Ramon-Esteve/polyphonic-synth/docs/bringup_vco_v2/photos/IMG_1949.jpeg

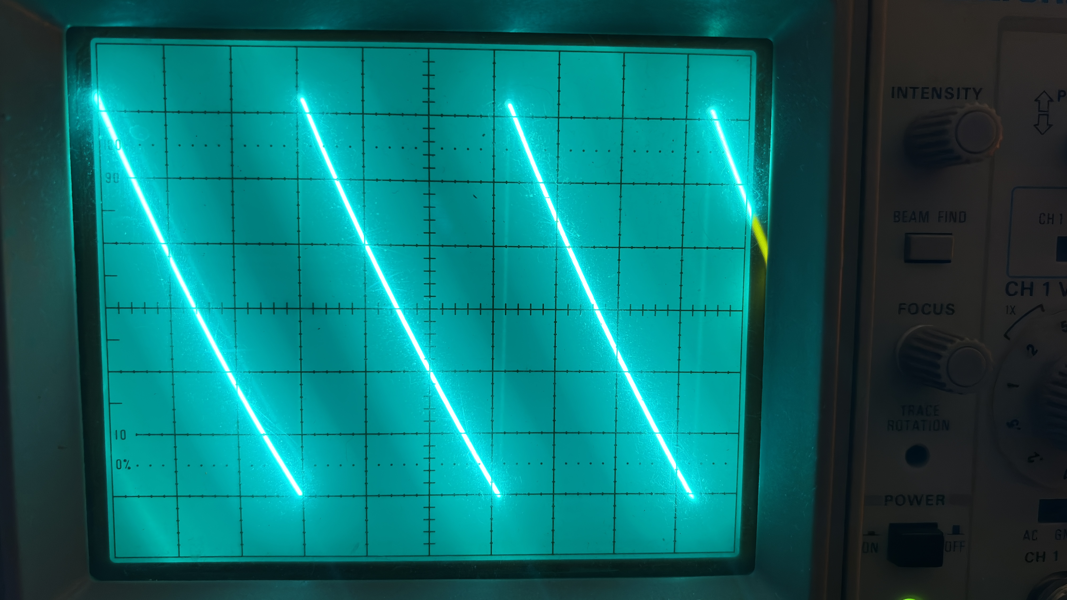
docs/bringup_vco_v2/photos/IMG_1949.jpeg
