Ramon-Esteve/polyphonic-synth/hardware/poly_synth_main/SYNTHH.kicad_sch

## KiCad design hardware/poly_synth_main/SYNTHH.kicad_sch (2026-06-09)

Schematic: SYNTHH.kicad_sch

Parts:
A1, A2: 10k; Potentiometer_Bourns_PTA6043_Single_Slide
ADJ_TUNE1, ADJ_TUNE2, ADJ_TUNE3: 1k; Potentiometer_Bourns_3266W_Vertical
AUDIO_OUT(3.5mm)1: AudioJack2_Ground_Switch; Jack_3.5mm_Cliff_FCR1281_Horizontal
C1, C10, C15: 2.2nF; C_Rect_L13.0mm_W4.0mm_P10.00mm_FKS3_FKP3_MKS4
C2, C11, C16: 1uF; C_Rect_L7.2mm_W5.0mm_P5.00mm
C3, C4, C5, C8, C9, C12, C13, C14, C17, C18, C19, C20, C21, C28, C29, C31, C32, C35, C36, C37, C38, C39, C40, C41, C42, C43, C44: 0.1uF; C_Disc_D5.1mm_W3.2mm_P5.00mm
C6, C7: 47uF; C_Radial_D5.0mm_H11.0mm_P2.00mm
C22, C30, C45: 1uF
C23, C24, C25, C26, C27: 1nF
C33: 0.33uF
C34: 0.1uF
COARSE1, COARSE2, COARSE3: 100k; Potentiometer_Omeg_PC16BU_Vertical
CUTOFF1: 100k; Potentiometer_Omeg_PC16BU_Vertical
CV_IN5: AudioJack2_Ground_Switch; Jack_3.5mm_Cliff_FCR1281_Horizontal
D1, D4, D5, D6, D7, D8, D9, D10, D11, D12, D13, D14, D15, D16: 1N4148; D_DO-35_SOD27_P7.62mm_Horizontal
D2, D3, D18, D19, D20: SB140; D_DO-41_SOD81_P10.16mm_Horizontal
D17, D21: 10k; Potentiometer_Bourns_PTA6043_Single_Slide
FINE1, FINE2, FINE3: 100k; Potentiometer_Omeg_PC16BU_Vertical
FM_IN3: AudioJack2_Ground_Switch; Jack_3.5mm_Cliff_FCR1281_Horizontal
FM_LVL3: 1M; Potentiometer_Omeg_PC16BU_Vertical
J1: DC_IN; TerminalBlock_RND_205-00288_1x03_P5.08mm_Horizontal
J2: USB_B
J3: AUDIO_OUT(6.35mm)
OFFSET1: 100k; Potentiometer_Omeg_PC16BU_Vertical
PWM1, PWM2, PWM3: 100k; Potentiometer_Omeg_PC16BU_Vertical
PWM_CV_LVL1, PWM_CV_LVL2, PWM_CV_LVL3: 250k; Potentiometer_Omeg_PC16BU_Vertical
PWM_IN1, PWM_IN2, PWM_IN3: AudioJack2_Ground_Switch; Jack_3.5mm_Cliff_FCR1281_Horizontal
Q1, Q4, Q6, Q7, Q8: BC548; TO-92_Inline
Q2, Q3, Q5: BC558; TO-92_Inline
Q-Point(Forward_Bias)1: 100k
R1, R5, R27, R31, R47, R51: 1M; R_Axial_DIN0207_L6.3mm_D2.5mm_P10.16mm_Horizontal
R2, R30, R50: 1k5; R_Axial_DIN0207_L6.3mm_D2.5mm_P10.16mm_Horizontal
R3, R22, R29, R32, R52, R62, R70, R71, R72, R74, R75, R76, R87, R89, R94, R96, R99, R100, R101, R103, R104, R105, R106, R107, R108, R110, R111, R112, R117, R118, R125, R126, R127, R128, R129, R132, R133, R134, R136, R137: 100k
R4, R6, R8, R9, R10, R12, R14, R19, R23, R25, R26, R28, R33, R34, R38, R39, R43, R45, R46, R48, R49, R53, R54, R58, R59: 100k; R_Axial_DIN0207_L6.3mm_D2.5mm_P10.16mm_Horizontal
R7, R24, R44: 33k; R_Axial_DIN0207_L6.3mm_D2.5mm_P10.16mm_Horizontal
R11, R37, R57: 47k; R_Axial_DIN0207_L6.3mm_D2.5mm_P10.16mm_Horizontal
R13, R16, R41, R63, R64, R65, R66, R67, R68, R69, R114, R138: 10k
R15, R17, R35, R40, R55, R60: 68k; R_Axial_DIN0207_L6.3mm_D2.5mm_P10.16mm_Horizontal
R18, R36, R56: 14k; R_Axial_DIN0207_L6.3mm_D2.5mm_P10.16mm_Horizontal
R20, R21: 10; R_Axial_DIN0207_L6.3mm_D2.5mm_P10.16mm_Horizontal
R42, R135: 10k; Potentiometer_Bourns_PTA6043_Single_Slide
R61, R78, R79, R81, R82, R83, R84, R85, R93: 33k
R73, R86: 27k
R77, R80: 2k
R88: 14k
R90, R91: 68k
R92, R95, R97, R130, R131: 1k
R98, R102, R109, R113, R123: 150k
R115, R116: 20k_Matched
R119, R120: 10k_MATCHED
R121, R122: 100k_MATCHED
R124: 100
RESO1: 100k; Potentiometer_Omeg_PC16BU_Vertical
RV1: 20k
R_pull_UP_SCL1: 4.7k
R_pull_UP_SDA1: 4.7k
S1, S2: 10k; Potentiometer_Bourns_PTA6043_Single_Slide
SOFTCLIP1: 100k; Potentiometer_Omeg_PC16BU_Vertical
SW1, SW3, SW5: SAW; Nidec_Copal_CAS-120A
SW2, SW4, SW6: PULSE; Nidec_Copal_CAS-120A
SW7: SUB; Nidec_Copal_CAS-120A
TH2, TH3, TH4, TH5, TH6, TH7, TH9, TH10, TH11, TH12: 10k; R_Axial_DIN0204_L3.6mm_D1.6mm_P5.08mm_Horizontal
U1: 40106; DIP-14_W7.62mm_Socket
U2, U4, U6: TL074; DIP-14_W7.62mm_Socket
U3, U5, U7, U8, U11, U13, U14, U15, U17: TL074
U9: NUCLEO-F446RE; MODULE_NUCLEO-F446RE; PARTREV 13
U10: L7805
U12: MCP4728; MSOP-10_3x3mm_P0.5mm
U16: ER_OLEDM0.91_1x-I2C
VCO1, VCO2, VCO3, VCO5, VCO6: 100k; Potentiometer_Omeg_PC16BU_Vertical
reso_intensity1: 50k; Potentiometer_Omeg_PC16BU_Vertical

Connections:
32DAC1 PA4: U9.CN7_32 (PA4), U13.2 (-)
+3.3V: A1.1, A2.1, D17.1, D18.2 (A), D19.2 (A), D20.2 (A), D21.1, R42.1, R135.1, R137.1, R_pull_UP_SCL1.1, R_pull_UP_SDA1.1, S1.1, S2.1, U9.CN7_16 (CN7_+3V3), U12.1 (VDD), U16.2 (VCC)
+12V: C3.1, C5.1, C6.1, C8.1, C12.1, C13.1, C18.1, C20.1, C28.1, C31.1, C33.2, C35.1, C37.1, C39.1, C41.1, C44.1, CUTOFF1.1, PWM1.1, PWM2.1, PWM3.1, Q-Point(Forward_Bias)1.1, R1.1, R9.2, R20.2, R23.2, R31.1, R43.2, R51.1, R115.1, R116.1, R128.1, U1.14 (VDD), U2.4 (V+), U3.4 (V+), U4.4 (V+), U5.4 (V+), U6.4 (V+), U7.4 (V+), U8.11 (V-), U10.1 (IN), U11.4 (V+), U13.4 (V+), U14.11 (V-), U15.4 (V+), U17.4 (V+)
-12V: C4.2, C7.2, C9.2, C14.2, C17.2, C19.2, C21.2, C29.2, C32.2, C36.2, C38.2, C40.2, C42.2, C43.2, CUTOFF1.3, PWM1.3, PWM2.3, PWM3.3, Q2.1 (C), Q3.1 (C), Q5.1 (C), Q-Point(Forward_Bias)1.3, R6.1, R7.1, R21.2, R24.1, R25.1, R44.1, R45.1, R87.1, U2.11 (V-), U3.11 (V-), U4.11 (V-), U5.11 (V-), U6.11 (V-), U7.11 (V-), U8.4 (V+), U11.11 (V-), U13.11 (V-), U14.4 (V+), U15.11 (V-), U17.11 (V-)
FEEDBACK: C23.1, C27.1, D15.2 (A), D16.1 (K), R96.1, U8.8
GND: A1.3, A2.3, ADJ_TUNE1.1, ADJ_TUNE1.2, ADJ_TUNE2.1, ADJ_TUNE2.2, ADJ_TUNE3.1, ADJ_TUNE3.2, AUDIO_OUT(3.5mm)1.G, AUDIO_OUT(3.5mm)1.S, C1.2, C3.2, C4.1, C5.2, C6.2, C7.1, C8.2, C9.1, C10.2, C12.2, C13.2, C14.1, C15.2, C17.1, C18.2, C19.1, C20.2, C21.1, C24.1, C25.1, C26.1, C28.2, C29.1, C31.2, C32.1, C33.1, C34.1, C35.2, C36.1, C37.2, C38.1, C39.2, C40.1, C41.2, C42.1, C43.1, C44.2, CV_IN5.G, CV_IN5.S, CV_IN5.T, D17.3, D21.3, FINE1.1, FINE2.1, FINE3.1, FM_IN3.G, FM_IN3.S, J1.2, J2.4 (GND), J2.SH (Shield), J3.S, OFFSET1.3, PWM_IN1.G, PWM_IN1.S, PWM_IN2.G, PWM_IN2.S, PWM_IN3.G, PWM_IN3.S, Q1.3 (E), Q4.3 (E), Q6.3 (E), R10.1, R11.1, R15.2, R18.1, R34.1, R36.1, R37.1, R40.2, R42.3, R54.1, R56.1, R57.1, R60.2, R73.1, R77.1, R84.2, R86.2, R94.2, R97.2, R117.2, R121.2, R124.2, R135.3, R136.1, RESO1.3, RV1.1, RV1.2, S1.3, S2.3, U1.7 (VSS), U1.9, U1.11, U1.13, U3.12 (+), U5.12 (+), U7.3 (+), U7.10 (+), U8.3 (+), U9.CN7_8 (CN7_GND), U9.CN7_19 (CN7_GND), U9.CN7_20 (CN7_GND), U9.CN7_22 (CN7_GND), U10.2 (GND), U12.4 (~LDAC), U12.10 (VSS), U14.3 (+), U14.5 (+), U15.3 (+), U16.1 (GND), U17.2 (-), U17.6 (-), U17.9 (-), U17.12 (+), VCO1.3, VCO2.3, VCO3.3, VCO5.3, VCO6.1, VCO6.3
MIXER: R3.1, R22.2, R29.2, R32.2, U3.13 (-)
unnamed: A1.2, U9.CN7_38 (PC0/PB8)
unnamed: A2.2, U9.CN7_28 (PA0)
unnamed: ADJ_TUNE1.3, R2.2
unnamed: ADJ_TUNE2.3, R30.2
unnamed: ADJ_TUNE3.3, R50.2
unnamed: AUDIO_OUT(3.5mm)1.T, R130.2
unnamed: C1.1, D1.1 (K), Q1.1 (C), U1.1, U2.3 (+)
unnamed: C2.1, U2.1, U2.2 (-)
unnamed: C2.2, R10.2, U2.5 (+), U2.10 (+)
unnamed: C10.1, D6.1 (K), Q4.1 (C), U1.3, U4.3 (+)
unnamed: C11.1, U4.1, U4.2 (-)
unnamed: C11.2, R34.2, U4.5 (+), U4.10 (+)
unnamed: C15.1, D8.1 (K), Q6.1 (C), U1.5, U6.3 (+)
unnamed: C16.1, U6.1, U6.2 (-)
unnamed: C16.2, R54.2, U6.5 (+), U6.10 (+)
unnamed: C22.1, U5.6 (-), U5.7
unnamed: C22.2, R76.1
unnamed: C23.2, D7.1 (K), D9.2 (A)
unnamed: C24.2, D9.1 (K), D10.2 (A)
unnamed: C25.2, D10.1 (K), D11.2 (A), U7.12 (+)
unnamed: C26.2, D11.1 (K), D12.2 (A)
unnamed: C27.2, D12.1 (K), D13.2 (A)
unnamed: C30.1, R93.2, U8.1
unnamed: C30.2, R94.1, U8.5 (+)
unnamed: C34.2, U9.CN7_6 (E5V), U10.3 (OUT)
unnamed: C45.1, R130.1, U15.8, U15.9 (-)
unnamed: C45.2, R62.1
unnamed: COARSE1.1, R9.1
unnamed: COARSE1.2, R8.1
unnamed: COARSE1.3, R7.2
unnamed: COARSE2.1, R23.1
unnamed: COARSE2.2, R26.1
unnamed: COARSE2.3, R24.2
unnamed: COARSE3.1, R43.1
unnamed: COARSE3.2, R46.1
unnamed: COARSE3.3, R44.2
unnamed: CUTOFF1.2, R89.1
unnamed: D1.2 (A), U1.2
unnamed: D2.1 (K), R20.1
unnamed: D3.2 (A), R21.1
unnamed: D4.1 (K), D5.2 (A), RV1.3
unnamed: D4.2 (A), D5.1 (K), R71.2, U5.3 (+)
unnamed: D6.2 (A), U1.4
unnamed: D7.2 (A), R79.2, R80.2
unnamed: D8.2 (A), U1.6
unnamed: D13.1 (K), R82.2, U7.7
unnamed: D14.1 (K), R81.1, R85.1, R86.1, R87.2
unnamed: D14.2 (A), R88.2, U7.8
unnamed: D15.1 (K), D16.2 (A), R96.2, U8.9 (-), reso_intensity1.3
unnamed: D17.2, U9.CN7_36 (PC1/PB9)
unnamed: D18.1 (K), R13.2, U9.CN10_4 (PC6)
unnamed: D19.1 (K), R16.2, U9.CN10_19 (PC7)
unnamed: D20.1 (K), R41.2, U9.CN10_2 (PC8)
unnamed: D21.2, U9.CN7_30 (PA1)
unnamed: FINE1.2, R5.1
unnamed: FINE1.3, R6.2
unnamed: FINE2.2, R27.1
unnamed: FINE2.3, R25.2
unnamed: FINE3.2, R47.1
unnamed: FINE3.3, R45.2
unnamed: FM_IN3.T, R49.1
unnamed: FM_LVL3.1, TH12.1
unnamed: FM_LVL3.2, FM_LVL3.3, Q5.2 (B), R50.1, TH9.1, TH10.1, TH11.1
unnamed: J2.2 (D-), U9.CN10_14 (PA11)
unnamed: J2.3 (D+), U9.CN10_12 (PA12)
unnamed: J3.T, R131.2
unnamed: OFFSET1.1, R128.2
unnamed: OFFSET1.2, R127.1
unnamed: PWM1.2, R19.1
unnamed: PWM2.2, R33.1
unnamed: PWM3.2, R53.1
unnamed: PWM_CV_LVL1.1, PWM_IN1.T
unnamed: PWM_CV_LVL1.2, PWM_CV_LVL1.3, R17.1
unnamed: PWM_CV_LVL2.1, PWM_IN2.T
unnamed: PWM_CV_LVL2.2, PWM_CV_LVL2.3, R35.1
unnamed: PWM_CV_LVL3.1, PWM_IN3.T
unnamed: PWM_CV_LVL3.2, PWM_CV_LVL3.3, R55.1
unnamed: Q1.2 (B), Q2.3 (E), R1.2
unnamed: Q2.2 (B), R2.1, TH2.1, TH3.1, TH4.1
unnamed: Q3.2 (B), R30.1, TH5.1, TH6.1, TH7.1
unnamed: Q3.3 (E), Q4.2 (B), R31.2
unnamed: Q5.3 (E), Q6.2 (B), R51.2
unnamed: Q7.1 (C), R115.2, R119.1
unnamed: Q7.2 (B), R117.1, R118.2
unnamed: Q7.3 (E), Q8.3 (E), R114.1
unnamed: Q8.1 (C), R116.2, R120.1
unnamed: Q8.2 (B), R124.1, R125.1
unnamed: Q-Point(Forward_Bias)1.2, R125.2
unnamed: R3.2, R52.1, U3.14
unnamed: R4.2, TH2.2
unnamed: R5.2, TH3.2
unnamed: R8.2, TH4.2
unnamed: R11.2, R12.2, U2.6 (-)
unnamed: R12.1, R64.1, U2.7
unnamed: R13.1, U17.1
unnamed: R14.1, R15.1, U2.12 (+)
unnamed: R14.2, U2.8
unnamed: R16.1, U17.7
unnamed: R17.2, R18.2, R19.2, U2.9 (-)
unnamed: R22.1, VCO1.2
unnamed: R26.2, TH5.2
unnamed: R27.2, TH6.2
unnamed: R28.2, TH7.2
unnamed: R29.1, VCO2.2
unnamed: R32.1, VCO3.2
unnamed: R33.2, R35.2, R36.2, U4.9 (-)
unnamed: R37.2, R38.2, U4.6 (-)
unnamed: R38.1, R65.1, U4.7
unnamed: R39.1, R40.1, U4.12 (+)
unnamed: R39.2, U4.8
unnamed: R41.1, U17.8
unnamed: R42.2, U9.CN7_34 (PB0)
unnamed: R46.2, TH9.2
unnamed: R47.2, TH10.2
unnamed: R48.2, TH11.2
unnamed: R49.2, TH12.2
unnamed: R52.2, R70.1, U5.13 (-)
unnamed: R53.2, R55.2, R56.2, U6.9 (-)
unnamed: R57.2, R58.2, U6.6 (-)
unnamed: R58.1, R67.1, U6.7
unnamed: R59.1, R60.1, U6.12 (+)
unnamed: R59.2, U6.8
unnamed: R61.1, R62.2, U15.13 (-)
unnamed: R63.1, SW2.1 (C)
unnamed: R64.2, SW1.1 (C)
unnamed: R65.2, SW3.1 (C)
unnamed: R66.1, SW4.1 (C)
unnamed: R67.2, SW5.1 (C)
unnamed: R68.1, SW6.1 (C)
unnamed: R69.2, SW7.1 (C)
unnamed: R70.2, R71.1, R75.1, U5.14
unnamed: R72.1, R73.2, U5.2 (-)
unnamed: R72.2, R74.1, U5.1
unnamed: R74.2, SOFTCLIP1.3
unnamed: R75.2, SOFTCLIP1.1
unnamed: R76.2, R77.2, U5.10 (+)
unnamed: R78.1, R83.1, U5.8, U5.9 (-)
unnamed: R78.2, R79.1, R81.2, U7.2 (-)
unnamed: R80.1, U7.1
unnamed: R82.1, R83.2, U7.6 (-)
unnamed: R84.1, R85.2, U7.5 (+)
unnamed: R88.1, R89.2, R90.2, R91.2, U7.9 (-)
unnamed: R90.1, VCO5.2
unnamed: R91.1, VCO6.2
unnamed: R92.1, RESO1.1, U7.13 (-), U7.14
unnamed: R92.2, R93.1, U8.2 (-)
unnamed: R95.1, U8.6 (-), U8.7
unnamed: R97.1, reso_intensity1.1, reso_intensity1.2
unnamed: R98.1, R99.2, U11.1
unnamed: R98.2, U11.3 (+)
unnamed: R99.1, U11.6 (-)
unnamed: R100.1, R101.2, U11.7
unnamed: R100.2, U11.5 (+)
unnamed: R102.1, R103.2, U11.8
unnamed: R102.2, U11.10 (+)
unnamed: R103.1, U11.13 (-)
unnamed: R104.1, R105.2, U11.14
unnamed: R104.2, U11.12 (+)
unnamed: R106.2, R107.1, U13.14
unnamed: R107.2, U13.12 (+)
unnamed: R108.1, U13.13 (-)
unnamed: R108.2, R109.1, U13.8
unnamed: R109.2, U13.10 (+)
unnamed: R110.2, R111.1, U14.14
unnamed: R111.2, U14.12 (+)
unnamed: R112.1, U14.13 (-)
unnamed: R112.2, R113.1, U14.8
unnamed: R113.2, U14.10 (+)
unnamed: R114.2, R126.2, U15.1
unnamed: R119.2, R122.1, U8.13 (-)
unnamed: R120.2, R121.1, U8.12 (+)
unnamed: R122.2, U8.14, U15.5 (+), U15.10 (+)
unnamed: R123.1, R132.2, U13.1
unnamed: R123.2, U13.3 (+)
unnamed: R126.1, R127.2, R129.2, U15.2 (-)
unnamed: R131.1, U15.6 (-), U15.7
unnamed: R132.1, U13.6 (-)
unnamed: R133.1, R134.2, U13.7
unnamed: R133.2, U13.5 (+)
unnamed: R135.2, U9.CN7_37 (PC3)
unnamed: R136.2, R137.2, U15.12 (+)
unnamed: R61.2, R138.1, U15.14
unnamed: R138.2, U9.CN10_34 (PC4)
unnamed: RESO1.2, U8.10 (+)
unnamed: S1.2, U9.CN7_35 (PC2)
unnamed: S2.2, U9.CN10_37 (PA3)
unnamed: SOFTCLIP1.2, U5.5 (+)
unnamed: SW1.2 (B), SW2.2 (B), U3.3 (+)
unnamed: SW3.2 (B), SW4.2 (B), U3.5 (+)
unnamed: SW5.2 (B), SW6.2 (B), SW7.2 (B), U3.10 (+)
unnamed: U3.1, U3.2 (-), VCO1.1
unnamed: U3.6 (-), U3.7, VCO2.1
unnamed: U3.8, U3.9 (-), VCO3.1
unnamed: U9.CN6_6 (CN6_GND), U9.CN6_7 (CN6_GND)
unnamed: U9.CN10_9 (CN10_GND), U9.CN10_20 (CN10_GND)
unnamed: U11.2 (-), U12.6 (VOUTA)
unnamed: U11.9 (-), U12.7 (VOUTB)
unnamed: U12.8 (VOUTC), U13.9 (-)
unnamed: U12.9 (VOUTD), U14.9 (-)
unnamed: U14.1, U14.2 (-)
unnamed: U14.6 (-), U14.7
unnamed: U17.13 (-), U17.14
PWR_IN_NEG: D3.1 (K), J1.1
PWR_IN_POS: D2.2 (A), J1.3
SCL: R_pull_UP_SDA1.2, U9.CN10_3 (PB8), U12.2 (SCL), U16.3 (SCL)
SDA: R_pull_UP_SCL1.2, U9.CN10_5 (PB9), U12.3 (SDA), U16.4 (SDA)
SIGNAL AMP IN: R95.2, R118.1
VCA CV: R129.1, R134.1
VCF VC: R110.1, VCO5.1
VCO2_TIME: R66.2, U4.13 (-), U4.14, U17.5 (+)
VCO3_TIME: R68.2, U6.13 (-), U6.14, U17.10 (+)
VCO 1 CV: R4.1, R101.1
VCO 2 CV: R28.1, R105.1
VCO 3 CV: R48.1, R106.1
VCO_01_TIME: R63.2, U2.13 (-), U2.14, U17.3 (+)

Notes on the sheet:
ENVELOPE
AUTOTUNE TIMER SIG & CLAMPER
inverting Adder: CV + Offset
CV-scaling Diode Offset?
DIODE CLIPPER
VCA -> OUT
VOut = 1+(100k/27k) = 4.7
(re)Invert Signal
BOOST SIGNAL TO LINE LVL (HEADROOM FOR RES)
Vout = -(V1 + V2 + V3) Rin = Rf = 100k -> unity gain
DIODE LADDER FILTER
VCO 2
VCO 3
scale down for diodes->
10Vpp
VCO 1
